BoujeeEnjinia1701/potholelog/docs/pdf/PHL-PRB-001_v0.7.pdf

P OT H O L E LO G · P R O B L E M S TAT E M E N T

# PotholeLog problem statement

Design Molecule Lab · designmolecule.com

D O C U M E N T CO N T RO L

Document ID | PHL-PRB-001 | Version | 0.7
Status | Draft | Date | 2026-10-02
Author | Amish Chadha | License | CERN-OHL-S-2.0
Project TRL | TRL 3 | Proof of concept
Repository | github.com/BoujeeEnjinia1701/potholelog
Source | docs/01-problem.md @ uncommitted

R EV I S I O N H I STO RY

Version | Date | Author | Change
0.7 | 2026-10-02 | Amish Chadha | Cost estimate USD 77.50 with the parts adopted on 2026-10-02
0.6 | 2026-10-02 | Amish Chadha | First pilot partner stated as decided on 2026-10-02 (PHL-DEC-001)
0.5 | 2026-10-01 | Amish Chadha | Budget treated as a value-engineering target
0.4 | 2026-09-25 | Amish Chadha | Recommendations accepted by Amish (DDR-002)
0.3 | 2026-09-25 | Amish Chadha | Reflect PHL-DDR-001 (floor mount, depot upload, privacy rule, bicycles deferred) and the tyre-bridging finding of PHL-CAL-001
0.2 | 2026-09-25 | Amish Chadha | Populate to TRL 2 (problem, users, context, constraints, prior work with sources)
0.1 | 2026-09-25 | Amish Chadha | Initial scaffold

D R A F T · N O T F O R F A B R I C A T I O N

## PotholeLog problem statement

Road surveys are expensive and infrequent, so repairs follow complaints rather than condition. Most cities and road agencies already run vehicles over every street each week, but those trips produce no record of the road surface. A low-cost logger on those vehicles could turn routine driving into a continuous, repeatable condition survey.

### The problem

Road condition data is collected in two main ways today, and both leave gaps.
Survey vehicles and profilers. Agencies measure roughness with instrumented vans or profilers and report it as the International Roughness Index (IRI), a standard scale the World Bank set out in 1986 (Sayers, Gillespie and Paterson, World Bank Technical Paper 46). (https://documents1.worldbank.org/curated/en/851131468160775725/pdf/multi-page.pdf) These surveys are accurate but are usually repeated only every year or several years, and local streets are surveyed least often.
Complaints and patrols. Potholes on local streets are mostly found by residents reporting them or by inspectors on foot or in a car. This favors busy and vocal neighborhoods and misses defects on routes that few people report.

The size of the gap is large even in well-funded networks. In the United States, about 25 % of the reported mileage of urban "other principal arterials" had an IRI above 170 in/mi (2.7 m/km) in 2023, the level the Federal Highway Administration treats as poor (computed from FHWA Highway Statistics 2023, table HM-64). (https://www.fhwa.dot.gov/policyinformation/statistics/2023/hm64.cfm) In England, local authorities rated 17 % of their unclassified roads, the small residential and rural roads, as needing maintenance to be considered in the year to March 2025 (DfT, Road conditions in England to March 2025). (https://www.gov.uk/government/statistics/road-conditions-in-england-to-march-2025)
Poor surfaces also matter for safety. About 1.16 million people die each year in road traffic crashes, 92 % of them in low- and middle-income countries, and more than half are pedestrians, cyclists and motorcyclists (WHO fact sheet). (https://www.who.int/news-room/fact-sheets/detail/road-traffic-injuries) Road surface is only one factor in those crashes, but it weighs most on two-wheelers, and it is the factor that condition data helps a maintenance team act on.

### Users and context

User | Need | Context
City or county road maintenance team | A map of where roads are rough and where new potholes appear, updated weekly, to plan patching and resurfacing | Small engineering team, limited survey budget, existing asset or GIS system
Fleet operator (transit agency, refuse contractor, municipal fleet) | A device that installs in minutes, needs no driver action and does not track drivers | Vehicles return to a depot daily; maintenance staff install and service devices
Drivers | No distraction, no performance monitoring | The device is out of sight and has no controls
Residents and cyclist groups | Evidence that repairs follow measured condition, not only complaints | Open data published by the city
Road agencies in low- and middle-income countries | Network condition data where survey vans are unaffordable | Mixed paved and unpaved roads, minibuses and trucks, intermittent connectivity

•

•

Operating context assumed for the concept:
Host vehicles are city buses, refuse trucks and similar fleet vehicles on fixed or repeated routes. They run about 8 to 12 h a day at 0 to 80 km/h and return to a depot each night (assumption).
The logger is bolted to a rigid point of the vehicle floor or structure above the rear axle and wired to the ignition-switched 12 V or 24 V supply (floor mount decided by Amish, 2026-09-25, PHL-DDR-001 D3).
A bus tyre about 1 m in diameter bridges much of a small pothole: it can drop only about 22 mm into one 300 mm long (PHL-CAL-001). Small potholes are therefore sought on slow passes, 10 to 30 km/h near stops and junctions (PHL-DDR-002), and larger ones at any speed.
Each street is driven many times a month by one or more vehicles, so results can be averaged over passes and vehicles.
The vehicle filters the road input through its tyres and suspension, and each vehicle responds differently, so the raw signal must be calibrated per vehicle before it can be compared with IRI.

### Prior work

Pothole Patrol (MIT, 2008). Accelerometers and GPS on 7 taxis in Boston. A simple classifier misidentified good road as potholes less than 0.2 % of the time, and after clustering over 90 % of reported potholes contained road anomalies needing repair (Eriksson et al., MobiSys 2008). (https://doi.org/10.1145/1378600.1378605) This is the closest precedent and shows the approach works on fleet vehicles.
Response-type roughness measuring systems. The World Bank IRI guidelines describe instruments that measure a vehicle's response to the road and convert it to IRI with a calibration equation found experimentally for that specific vehicle (World Bank Technical Paper 46). (https://documents1.worldbank.org/curated/en/851131468160775725/pdf/multi-page.pdf) PotholeLog follows the same principle with a cheaper sensor.
Smartphone apps. Several cities and development agencies have used phone apps to log bumps and roughness. Phones are cheap but move in their mounts, change between trips and depend on a volunteer; a fixed, calibrated logger avoids those problems.

### Constraints

Garage-buildable prototype, with parts cost judged against a value-engineering target of about $75 USD per unit
( budget_usd | in | project.yaml , a hypothetical control target, raised from $70 under PHL-DDR-002 to cover a
60 V converter); the constructable design is estimated at $77.50 with the status lights, breather vent and nameplate adopted on 2026-10-02, $2.50 over the target.
Off-the-shelf modules only; no custom PCB for the first build.
Installs on a fleet vehicle without cutting or welding structural members and without the driver doing anything. Road data only: no camera, no microphone, and no driver behavior scoring. Only road-segment roughness and defect clusters are published; vehicle tracks and timestamps stay on the operator's server (privacy rule decided by Amish, 2026-09-25).
This build serves buses and refuse trucks; a bicycle variant is a later step (PHL-DDR-001, D1).
Open hardware (CERN-OHL-S-2.0) and open software (MIT), with outputs in open formats (CSV, GeoJSON).

### Out of scope

Replacing a calibrated profiler for pavement design or contract acceptance.

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
Measuring crack type, rutting depth or skid resistance.
Real-time alerts to drivers.

Safety: The logger is installed on vehicles that operate in traffic and are connected to a vehicle electrical system. Mounting, wiring and fusing must follow the fleet operator's procedures. See the precis (PHL-PRC-001) for the full safety section.

### User research and co-design

This design is for communities the author is not part of, so requirements come from the people who will use it.
[ ] Identify a local partner organization (Helpful Engineering network, NGO or university); the first pilot partner to approach is a Dallas-Fort Worth area city with its own bus or refuse fleet, with TxDOT pavement management roughness data on state roads in that city as the reference IRI sections (decided 2026-10-02, PHL-DEC-001) [ ] Run co-design sessions with intended users; record who, where and what was learned
[ ] Validate load, distance, terrain and cost assumptions in the field
[ ] Revise requirements (REQ) from findings before freezing the design

•
•

•

•
•
•
