BoujeeEnjinia1701/potholelog/cad/drawings/PHL-DWG-001.pdf

CONCEPT, NOT FOR FABRICATION | PotholeLog · github.com/BoujeeEnjinia1701/potholelog

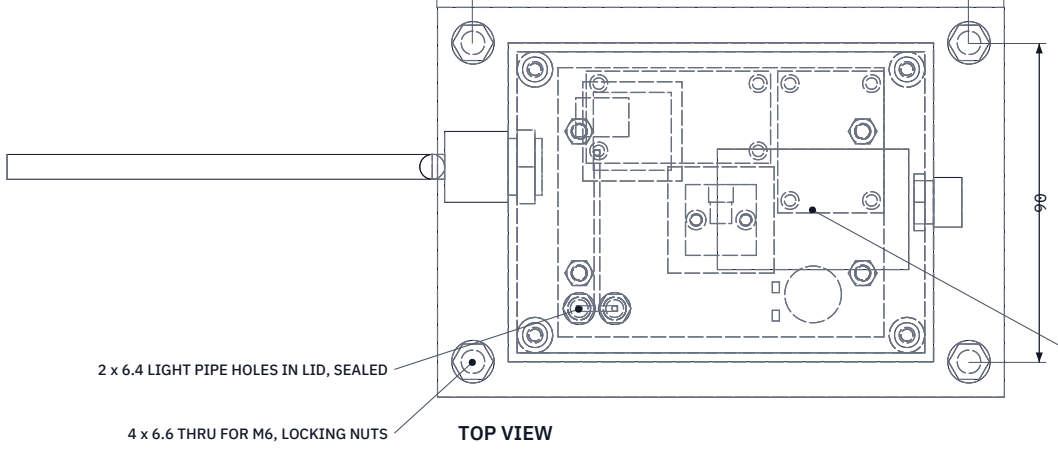
[picture p32: figure]
TOP VIEW; 4 x 6.6 THRU FOR M6, LOCKING NUTS

FRONT VIEW
Scale 1:2; looking at the front (along +Y)

Scale 1:2; looking down (along -Z)

RIGHT VIEW
Scale 1:2; looking at the right side (along -X)

282

110 62

VEHICLE FLOOR OR RAIL

55 BOX

IMU ON BOX FLOOR, CENTER 7.3 ABOVE FLOOR

M16 GLAND, FUSED LEAD TO IGNITION FEED | GNSS UNDER LID, SKY VIEW UP

M12 BREATHER VENT, 12.2 HOLE IN FRONT WALL

140

160

FORWARD +X

2 x 6.4 LIGHT PIPE HOLES IN LID, SEALED | NAMEPLATE LABEL, ARROW FORWARD
90 | ISOMETRIC VIEW Not to scale; seen from the front right and above, about 30 deg elevation

MAIN DIMENSIONS AND INTERFACES (MM)
Plate Al 5052 160 x 110 x 4; 4 x M6 on 140 x 90
Stock IP65 box 120 x 90 x 55; 4 x M4 hex standoffs into plate on 80 x 40 Modules on a 92 x 76 x 1.5 Al carrier on the standoffs
Overall height 59 on the floor; logger about 0.44 kg
Bolt at existing floor, seat-rail or crossmember fixings
Plate first mode about 168 Hz on corner bolts (PHL-CAL-001)
IMU on box floor, 2 x M3 into plate; X axis forward
GNSS under lid; 2 light pipes in lid; M12 vent in front wall
Supply 9 to 36 V, converter rated 60 V; fused 2 A, ignition switched; 0.54 W Third-angle; front view from -Y; X forward along the vehicle
REV | DESCRIPTION | DATE | BY
P1 | Preliminary GA for TRL 3 (from cad/src/model.py) | 2026-09-25 | AC
P2 | Supply note: 60 V converter (PHL-DDR-002) | 2026-09-25 | AC
P3 | Constructable design: standoffs, carrier, IMU screws (PHL-DDR-003) | 2026-10-01 | AC
P4 | Light pipes, breather vent, nameplate (PHL-DEC-001) | 2026-10-02 | AC
POTHOLELOG | github.com/BoujeeEnjinia1701/potholelog

## General arrangement

DRAWING NO.
PHL-DWG-001

REV
P4

SHEET
1 of 1

SIZE

## ANSI B

SCALE
1:2

UNITS
mm
PROJECTION | DATE
2026-10-02

DRAWN
Amish Chadha

MATERIAL / NOTES
Al 5052 plate; stock IP65 box; bought-in parts per bom/bom.csv. PRELIMINARY, NOT FOR FABRICATION
Licensed CERN-OHL-S-2.0 · Design Molecule Lab · designmolecule.com | Generated from cad/src; do not edit by hand
