BoujeeEnjinia1701/potholelog/cad/drawings/PHL-DWG-101.pdf

BUILD PLAN SKETCH, PLAN NOT YET BUILT PotholeLog · github.com/BoujeeEnjinia1701/potholelog

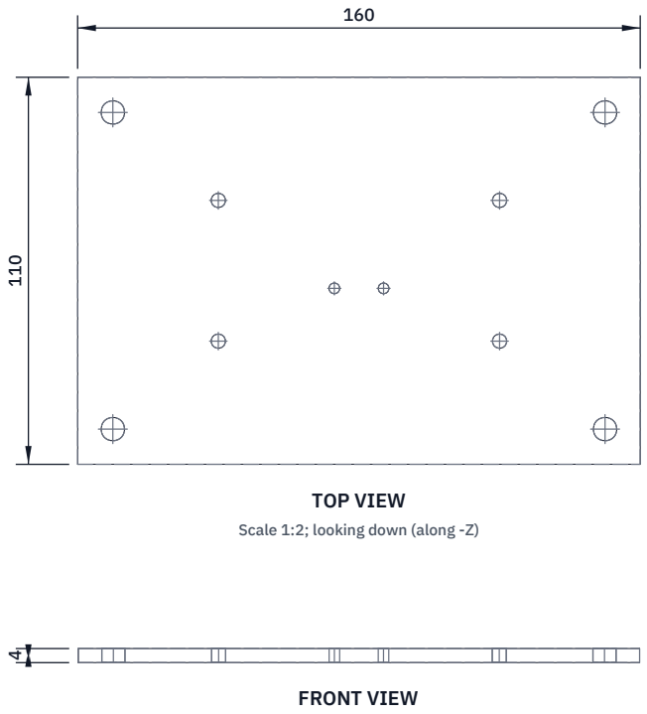
[picture p33: figure]
FRONT VIEW; TOP VIEW; Scale 1:2; looking down (along -Z)

Scale 1:2; looking at the front (along +Y)

RIGHT VIEW
Scale 1:2; looking at the right side (along -X)

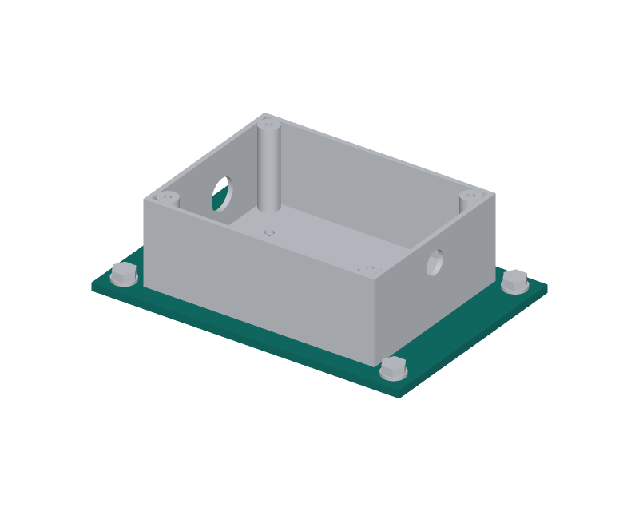
[picture p34: figure]

WHERE IT GOES
This part in colour, its neighbours in grey

HOW TO MAKE IT AND HOW IT FITS
Blank 160 x 110 mm, 4 mm aluminium. Square the edges, deburr, round the corners to about 2 mm. Measure every hole from the plate's centre lines; the hole layout picture repeats them.
Corner holes: four 6.6 mm (M6 clearance), 70 mm each side along the length and 45 mm each side across (140 x 90 mm apart).
Box standoff holes: four M4 tapped, drill 3.3 mm and tap,
40 mm each side along and 20 mm each side across (80 x 40 apart). IMU holes: two M3 tapped, drill 2.5 mm and tap, 7 mm each side of the cross centre line, 5 mm to the right of the long centre line. Better: drill the IMU and standoff holes through the box floor
with the box clamped on the plate, then open the floor holes.
Fit: the box floor sits flat on the top face; nothing may stick out below the plate, so the standoffs and screws stop inside it. Check: every tapped hole takes its screw by hand.
REV | DESCRIPTION | DATE | BY
P1 | Making sketch for the prototype build plan | 2026-10-02 | AC
POTHOLELOG | github.com/BoujeeEnjinia1701/potholelog

## PotholeLog mounting plate: making sketch

DRAWING NO.
PHL-DWG-101

REV
P1

SHEET
1 of 1

SIZE

## ANSI B

SCALE
1:2

UNITS
mm
PROJECTION | DATE
2026-10-02

DRAWN
Amish Chadha

MATERIAL / NOTES
Aluminium sheet 4 mm, 5052
Licensed CERN-OHL-S-2.0 · Design Molecule Lab · designmolecule.com | Generated from cad/src; do not edit by hand
