BoujeeEnjinia1701/potholelog/cad/drawings/PHL-DWG-102.pdf

BUILD PLAN SKETCH, PLAN NOT YET BUILT PotholeLog · github.com/BoujeeEnjinia1701/potholelog

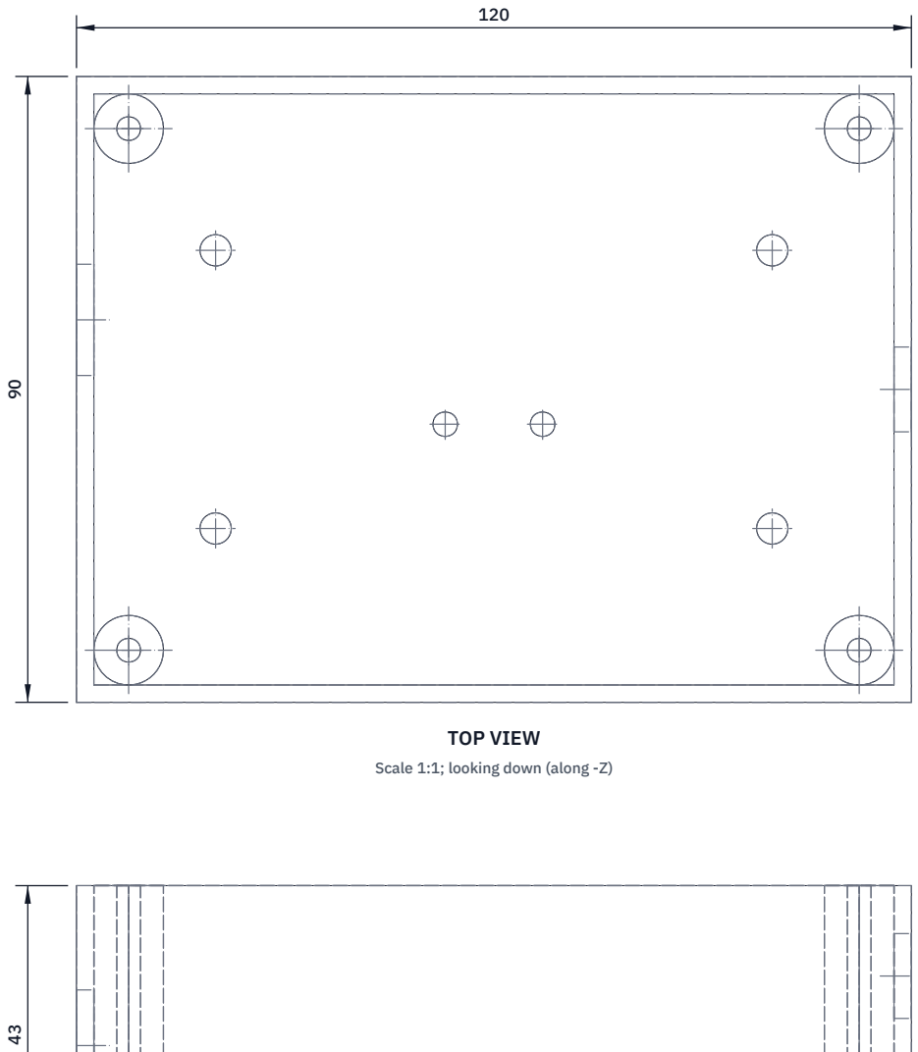
[picture p35: figure]
TOP VIEW; Scale 1:1; looking down (along -Z)
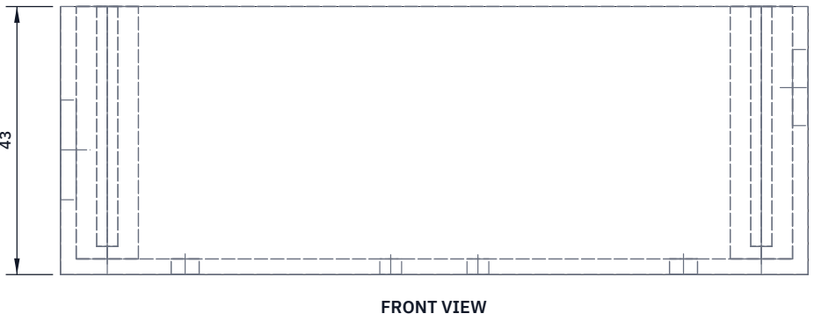
[picture p36: figure]
FRONT VIEW

Scale 1:1; looking at the front (along +Y)

RIGHT VIEW
Scale 1:1; looking at the right side (along -X)

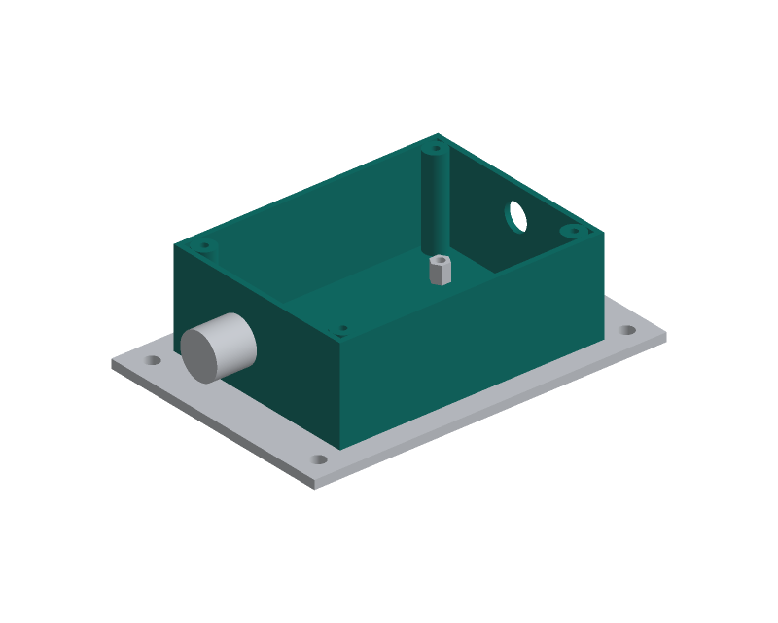
[picture p37: figure]

WHERE IT GOES
This part in colour, its neighbours in grey

HOW TO MAKE IT AND HOW IT FITS
Bought box with four moulded corner pillars for the lid screws. Floor, measured from its centre, front is away from the gland:
four 4.5 mm holes 40 mm each side along, 20 mm each side across; two 3.5 mm holes 7 mm each side of centre, 5 mm to the right. The floor holes must match the plate's tapped holes: drill
them through the plate's holes with the box clamped on it.
Rear end wall: one 16.2 mm hole for the M16 gland, 10 mm left of centre, its centre 20 mm up from the box's underside.
Front end wall: one 12.2 mm hole for the M12 breather vent, on the centre line, its centre 30 mm up from the underside. Tape the faces, pilot 3 mm at low speed with wood behind, open out with a step drill. No solvents: polycarbonate crazes.
Fit: the floor sits flat on the plate; a ring of neutral-cure
silicone round each floor hole underneath seals it.
Check: no crack runs from any hole under a bright lamp.
REV | DESCRIPTION | DATE | BY
P1 | Making sketch for the prototype build plan | 2026-10-02 | AC
POTHOLELOG | github.com/BoujeeEnjinia1701/potholelog

## PotholeLog enclosure base: drilling sketch

DRAWING NO.
PHL-DWG-102

REV
P1

SHEET
1 of 1

SIZE

## ANSI B

SCALE
1:1

UNITS
mm
PROJECTION | DATE
2026-10-02

DRAWN
Amish Chadha

MATERIAL / NOTES
Bought IP65 polycarbonate box 120 x 90 x 55 mm
Licensed CERN-OHL-S-2.0 · Design Molecule Lab · designmolecule.com | Generated from cad/src; do not edit by hand
