BoujeeEnjinia1701/potholelog/cad/drawings/PHL-DWG-103.pdf

BUILD PLAN SKETCH, PLAN NOT YET BUILT PotholeLog · github.com/BoujeeEnjinia1701/potholelog

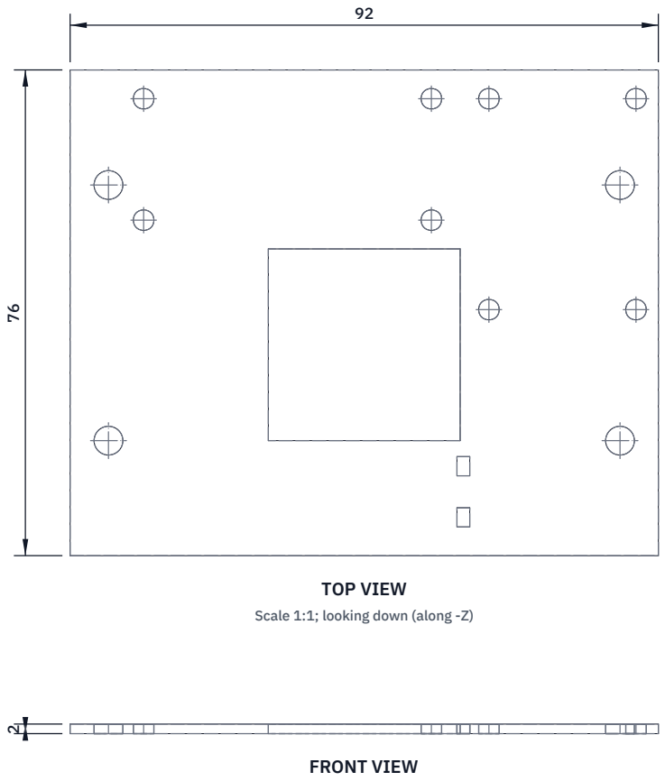
[picture p38: figure]
FRONT VIEW; TOP VIEW; Scale 1:1; looking down (along -Z)

Scale 1:1; looking at the front (along +Y)

RIGHT VIEW
Scale 1:1; looking at the right side (along -X)

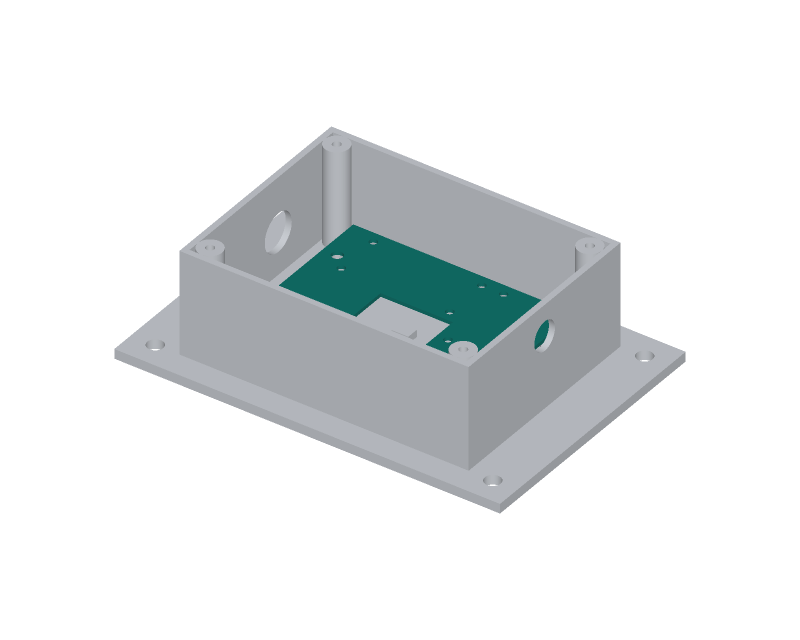
[picture p39: figure]

WHERE IT GOES
This part in colour, its neighbours in grey

HOW TO MAKE IT AND HOW IT FITS
Blank 92 x 76 mm, 1.5 mm aluminium; deburr all edges.
Window 30 x 30 mm over the IMU, centred 5 mm right of centre: drill 6 mm in each corner, cut between with a piercing saw, file. Fixing holes: four 4.5 mm, 80 x 40 mm apart, matching the plate. Module holes: 3.2 mm; mark them through each module (about 23 x 33 mm for the converter, 45 x 19 mm for the controller). Tie slots: two 2 x 3 mm, 15.5 mm forward of centre, 24 and
32 mm right of centre, for the supercapacitor's cable tie.
Fit: sits on the four hex standoffs 8 mm above the box floor, held by four M4 x 6 screws; 1.5 mm clear of the walls and pillars, 4.5 mm clear of the gland locknut.
Check: drops onto the standoffs without touching a wall.
REV | DESCRIPTION | DATE | BY
P1 | Making sketch for the prototype build plan | 2026-10-02 | AC
POTHOLELOG | github.com/BoujeeEnjinia1701/potholelog

## PotholeLog module carrier plate: making sketch

DRAWING NO.
PHL-DWG-103

REV
P1

SHEET
1 of 1

SIZE

## ANSI B

SCALE
1:1

UNITS
mm
PROJECTION | DATE
2026-10-02

DRAWN
Amish Chadha

MATERIAL / NOTES
Aluminium sheet 1.5 mm, 5052
Licensed CERN-OHL-S-2.0 · Design Molecule Lab · designmolecule.com | Generated from cad/src; do not edit by hand
