BoujeeEnjinia1701/potholelog/cad/drawings/PHL-DWG-104.pdf

BUILD PLAN SKETCH, PLAN NOT YET BUILT PotholeLog · github.com/BoujeeEnjinia1701/potholelog

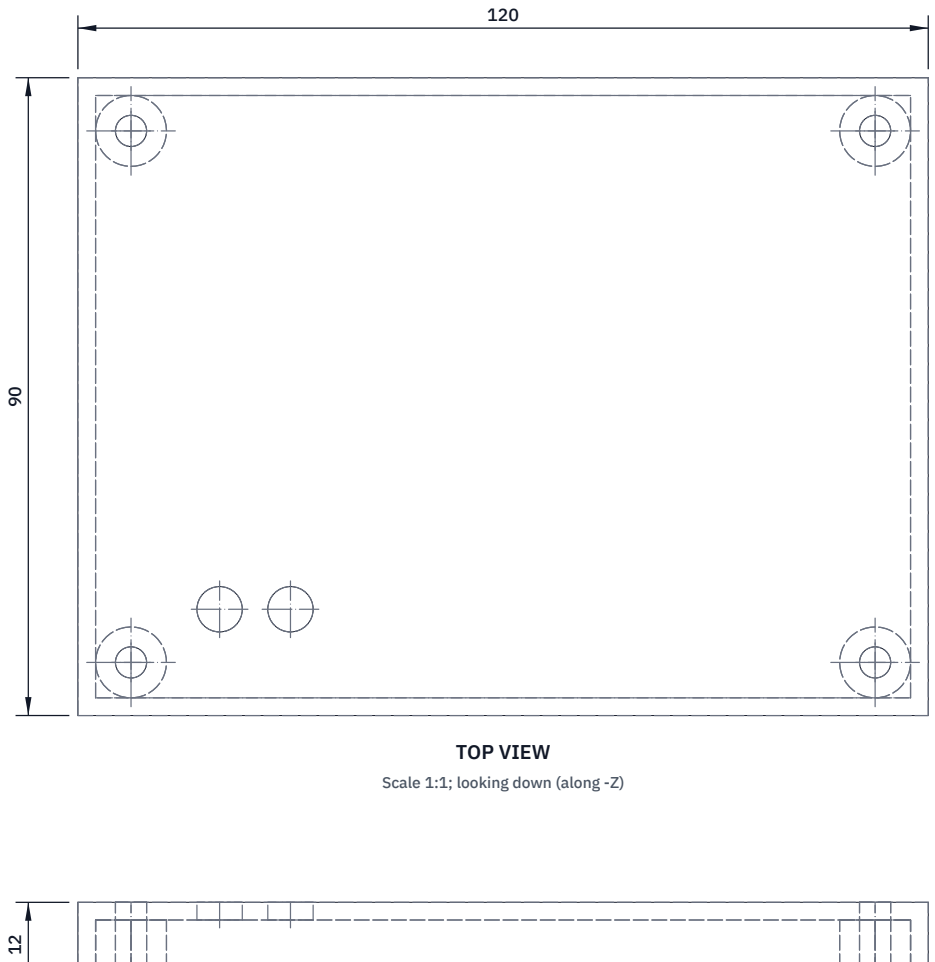
[picture p40: figure]
TOP VIEW; Scale 1:1; looking down (along -Z)

FRONT VIEW
Scale 1:1; looking at the front (along +Y)

RIGHT VIEW
Scale 1:1; looking at the right side (along -X)

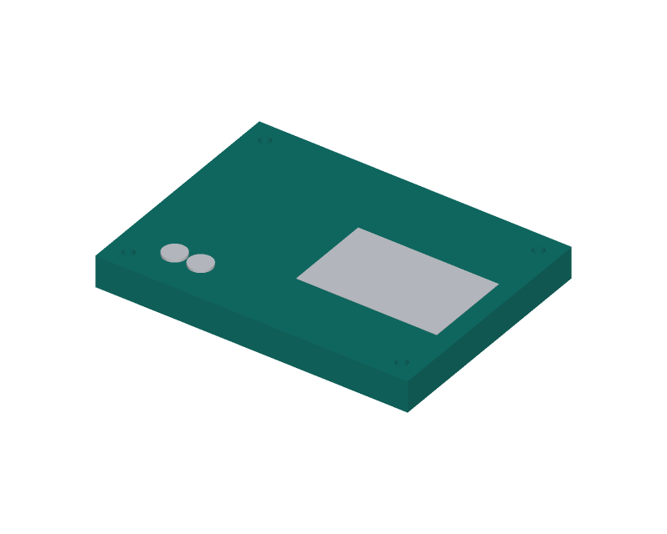
[picture p41: figure]

WHERE IT GOES
This part in colour, its neighbours in grey

HOW TO MAKE IT AND HOW IT FITS
Lid of the bought box, opaque, with its gasket and corner pillars. Two 6.4 mm holes for the sealed light pipes, measured
from the lid's centre: 40 and 30 mm toward the rear (gland) end, both 30 mm to the right of the long centre line.
Rear hole: power light; front hole: logging light.
Tape the top, pilot 3 mm with wood behind, open out with a
step drill; check the size against the light pipe's datasheet.
Keep 25 mm round the GNSS module's patch free of labels and metal. Nameplate label 54 x 34 mm, centred 26 mm forward,
arrow pointing forward, on the cleaned lid top.
Fit: each pipe's O-ring under its flange outside, nut inside.
Check: no crack from either hole; the nuts clear the pillars.
REV | DESCRIPTION | DATE | BY
P1 | Making sketch for the prototype build plan | 2026-10-02 | AC
POTHOLELOG | github.com/BoujeeEnjinia1701/potholelog

## PotholeLog enclosure lid: drilling sketch

DRAWING NO.
PHL-DWG-104

REV
P1

SHEET
1 of 1

SIZE

## ANSI B

SCALE
1:1

UNITS
mm
PROJECTION | DATE
2026-10-02

DRAWN
Amish Chadha

MATERIAL / NOTES
Lid of the bought IP65 box (opaque)
Licensed CERN-OHL-S-2.0 · Design Molecule Lab · designmolecule.com | Generated from cad/src; do not edit by hand
