BoujeeEnjinia1701/potholelog/media/card.png

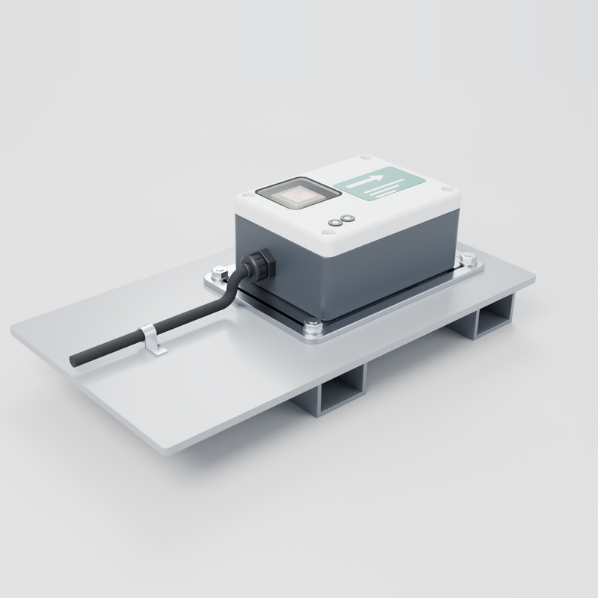
media/card.png
