BoujeeEnjinia1701/potholelog/media/render-detail.png

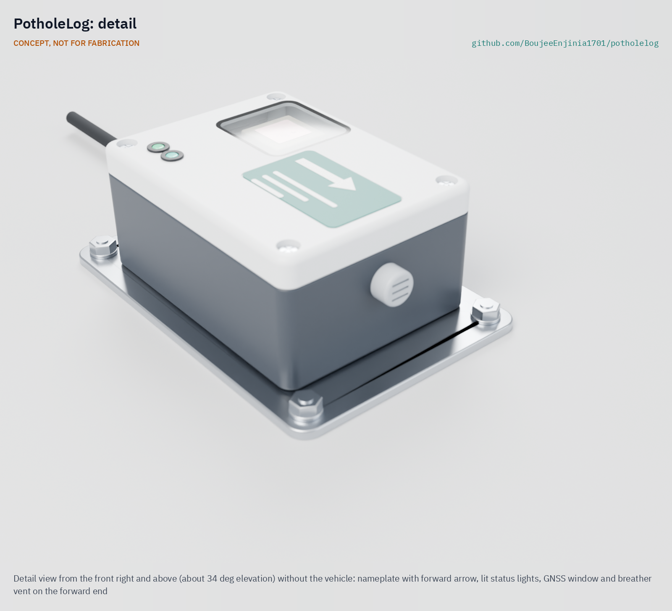
media/render-detail.png
