BoujeeEnjinia1701/potholelog/media/render-exploded.png

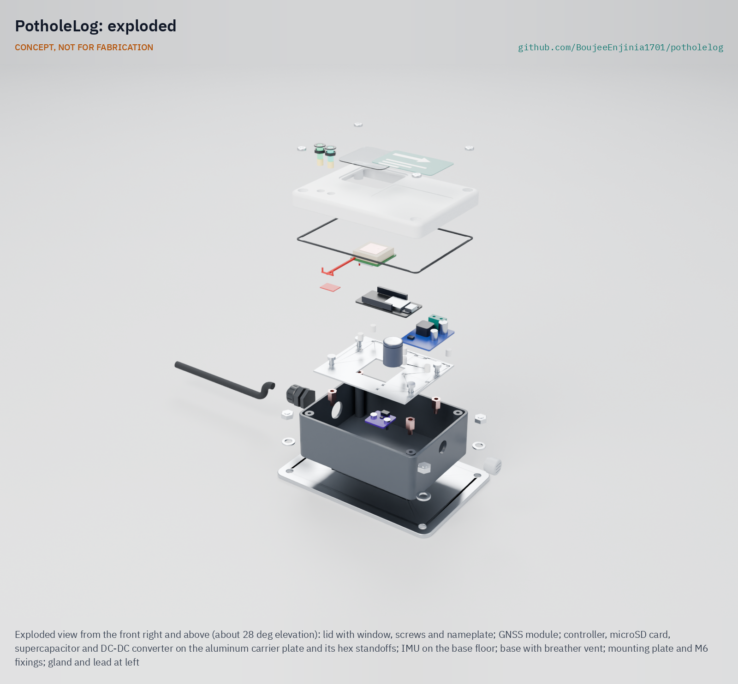
media/render-exploded.png
