BoujeeEnjinia1701/potholelog/media/social-preview.png

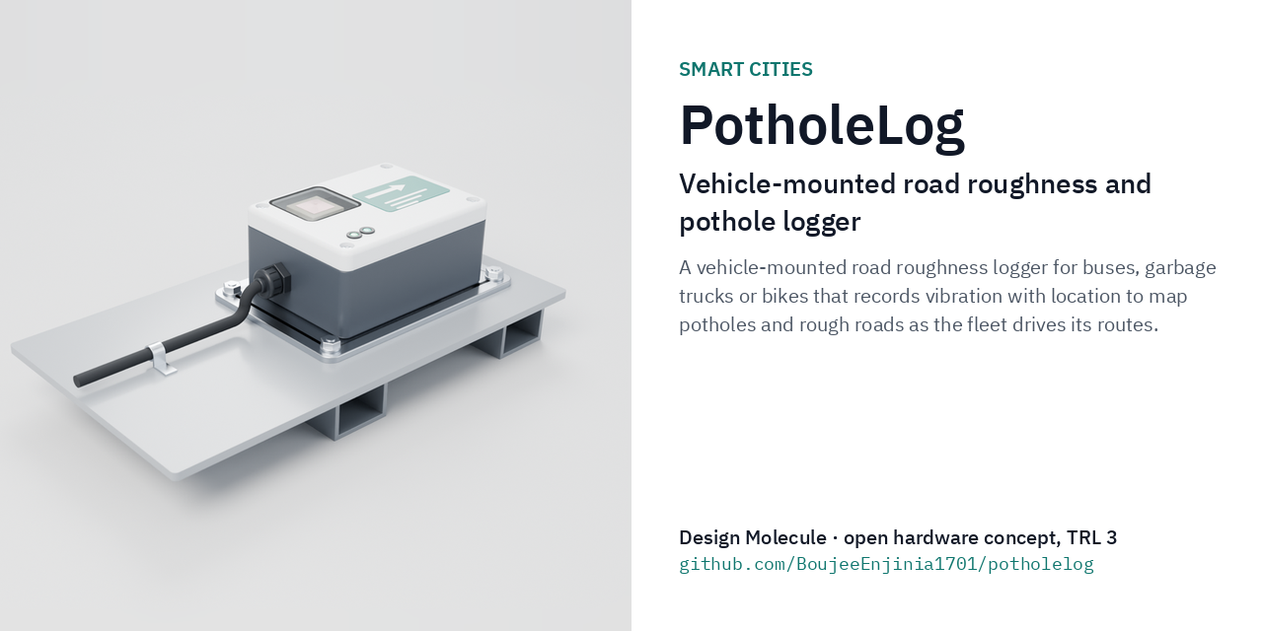
media/social-preview.png
